arkadiuszmakarenko/RISKYSpeccy/firmware/User/ch32v30x_it.h

/********************************** (C) COPYRIGHT *******************************
* File Name          : ch32v30x_it.h
* Author             : WCH
* Version            : V1.0.0
* Date               : 2021/06/06
* Description        : This file contains the headers of the interrupt handlers.
*********************************************************************************
* Copyright (c) 2021 Nanjing Qinheng Microelectronics Co., Ltd.
* Attention: This software (modified or not) and binary are used for 
* microcontroller manufactured by Nanjing Qinheng Microelectronics.
*******************************************************************************/
#ifndef __CH32V30x_IT_H
#define __CH32V30x_IT_H

#include "debug.h"

void EXTI9_5_IRQHandler(void) __attribute__((interrupt("WCH-Interrupt-fast")));
void EXTI15_10_IRQHandler(void) __attribute__((interrupt("WCH-Interrupt-fast")));


#endif /* __CH32V30x_IT_H */
